qutefox/SensorFusion/software/src/processor_logic/fusion_data.cpp

#include "fusion_data.h"

#include "mxc_lock.h"

#include "src/storage/register_map.h"
#include "src/sensor_fusion_board.h"
#include "src/sensor/lsm6dsm.h"
#include "src/debug_print.h"

FusionData* FusionData::instance = nullptr;
uint32_t FusionData::lock = 0;

FusionData::FusionData()
    : register_map{ storage::RegisterMap::get_instance() }
    , register_map_helper{ storage::RegisterMapHelper::get_instance(register_map) }
    , calibration_data{ CalibrationData::get_instance() }
    , quaternion_fqvect{ FUSION_IDENTITY_QUATERNION }
    , euler{ FUSION_EULER_ZERO }
    , earth{ FUSION_VECTOR_ZERO }
    , gyroscope_fvect{ FUSION_VECTOR_ZERO }
    , accelerometer_fvect{ FUSION_VECTOR_ZERO }
    , magnetometer_fvect{ FUSION_VECTOR_ZERO }
    , pressure{ 0 }
    , temperature{ 0 }
    , timestamp{ 0 }
    , previous_timestamp{ 0 }
    , has_new_quaternion_data{ false }
    , has_new_euler_data{ false }
    , has_new_earth_data{ false }
    , has_new_pressure_data{ false }
    , has_new_temperature_data{ false }
    , has_new_gyroscope_data{ false }
    , has_new_accelerometer_data{ false }
    , has_new_magnetometer_data{ false }
    , use_calibration_data{ false }
    , euler_output_enabled{ false }
    , earth_output_enabled{ false }
    , ahrs_error{ false }
    , ahrs_gyro_error{ false }
    , ahrs_accel_error{ false }
    , ahrs_mag_error{ false }
{
    FusionAhrsInitialise(&ahrs);

    if (CONTROL1_REGISTER_DEFAULT_VALUE & CONTROL1_REGISTER_EULER_MASK)
    {
        euler_output_enabled = true;
    }

    if (CONTROL1_REGISTER_DEFAULT_VALUE & CONTROL1_REGISTER_EARTH_MASK)
    {
        earth_output_enabled = true;
    }

    if (CONTROL2_REGISTER_DEFAULT_VALUE & CONTROL2_REGISTER_CALIBRATION_ACTIVE_MASK)
    {
        use_calibration_data = true;
    }

    update_calibration_data();

    // Cannot call reset here, because the SensorBase class constructs the fusion data (this class)
    // before the SensorFusionBoard class does.
    // Meaning that the board pointer is nullptr here and now.
    // Inside the reset() function we use the board class to get the sensor pointer
    // to read the data rate (board->inertial_sensor->get_data_rate()).
    // This causes a nullpointer exception.
    // The Controller class will call reset when starting the fusion.
    // reset();
}

FusionData::~FusionData()
{
    FusionAhrsReset(&ahrs);
}

FusionData* FusionData::get_instance()
{
    MXC_GetLock(&lock, 1);
    if (instance == nullptr)
    {
        instance = new FusionData();
    }
    MXC_FreeLock(&lock);
    return instance;
}

void FusionData::reset()
{
    uint16_t gyro_sample_rate = 100;

    sensor::SensorInterface* sensor = nullptr;
    SensorFusionBoard* board = SensorFusionBoard::get_instance();
    if (board != nullptr)
    {
        sensor = board->get_inertial_sensor();
    }
    
    if (sensor != nullptr)
    {
        gyro_sample_rate = sensor->get_sample_rate_in_hz(sensor::Lsm6dsmDevice::LSM6DSM_DEVICE_GYRO);
        if (gyro_sample_rate == 0) gyro_sample_rate = 100;
    }

    FusionOffsetInitialise(&ahrs_offset, gyro_sample_rate);

    // Set AHRS algorithm settings.
    const FusionAhrsSettings settings = {
        .convention = FusionConventionNwu,
        .gain = 0.5f,
        .gyroscopeRange = 500.0f, // gyroscope range in degrees/s
        .accelerationRejection = 10.0f,
        .magneticRejection = 10.0f,
        .recoveryTriggerPeriod = 5 * gyro_sample_rate, // 5 seconds
    };
    FusionAhrsSetSettings(&ahrs, &settings);

    FusionAhrsReset(&ahrs);
    
    has_new_quaternion_data = false;
    has_new_euler_data = false;
    has_new_earth_data = false;
    has_new_pressure_data = false;
    has_new_temperature_data = false;
    has_new_gyroscope_data = false;
    has_new_accelerometer_data = false;
    has_new_magnetometer_data = false;

    ahrs_error = false;
    ahrs_gyro_error = false;
    ahrs_accel_error = false;
    ahrs_mag_error = false;
}

void FusionData::update_register_map()
{
    if (register_map_helper->is_quaternion_data_read_by_host())
    {
        if (has_new_quaternion_data)
        {
            register_map_helper->write_quaternion_data(quaternion_fqvect);
            has_new_quaternion_data = false;
            register_map_helper->set_quaternion_data_ready_flag(true);
        }
        else
        {
            register_map_helper->set_quaternion_data_ready_flag(false);
        }
    }

    if (register_map_helper->is_euler_data_read_by_host())
    {
        if (has_new_euler_data)
        {
            register_map_helper->write_euler_data(euler);
            has_new_euler_data = false;
            register_map_helper->set_euler_data_ready_flag(true);
        }
        else
        {
            register_map_helper->set_euler_data_ready_flag(false);
        }
    }

    if (register_map_helper->is_earth_data_read_by_host())
    {
        if (has_new_earth_data)
        {
            register_map_helper->write_earth_data(earth);
            has_new_earth_data = false;
            register_map_helper->set_earth_data_ready_flag(true);
        }
        else
        {
            register_map_helper->set_earth_data_ready_flag(false);
        }
    }

    if (register_map_helper->is_gyroscope_data_read_by_host())
    {
        if (has_new_gyroscope_data)
        {
            register_map_helper->write_gyroscope_data(gyroscope_fvect);
            has_new_gyroscope_data = false;
            register_map_helper->set_gyroscope_data_ready_flag(true);
        }
        else
        {
            register_map_helper->set_gyroscope_data_ready_flag(false);
        }
    }

    if (register_map_helper->is_accelerometer_data_read_by_host())
    {
        if (has_new_accelerometer_data)
        {
            register_map_helper->write_accelerometer_data(accelerometer_fvect);
            has_new_accelerometer_data = false;
            register_map_helper->set_accelerometer_data_ready_flag(true);
        }
        else
        {
            register_map_helper->set_accelerometer_data_ready_flag(false);
        }
    }

    if (register_map_helper->is_magnetometer_data_read_by_host())
    {
        if (has_new_magnetometer_data)
        {
            register_map_helper->write_magnetometer_data(magnetometer_fvect);
            has_new_magnetometer_data = false;
            register_map_helper->set_magnetometer_data_ready_flag(true);
        }
        else
        {
            register_map_helper->set_magnetometer_data_ready_flag(false);
        }
    }

    if (register_map_helper->is_pressure_data_read_by_host())
    {
        if (has_new_pressure_data)
        {
            register_map_helper->write_pressure_data(pressure);
            has_new_pressure_data = false;
            register_map_helper->set_pressure_data_ready_flag(true);
        }
        else
        {
            register_map_helper->set_pressure_data_ready_flag(false);
        }
    }

    if (register_map_helper->is_temperature_data_read_by_host())
    {
        if (has_new_temperature_data)
        {
            register_map_helper->write_temperature_data(temperature);
            has_new_temperature_data = false;
            register_map_helper->set_temperature_data_ready_flag(true);
        }
        else
        {
            register_map_helper->set_temperature_data_ready_flag(false);
        }
    }
}

void FusionData::set_use_calibration_data(bool use)
{
    use_calibration_data = use;
}

void FusionData::set_euler_output_enable(bool enable)
{
    if (!enable)
    {
        register_map_helper->set_euler_data_ready_flag(false);
        has_new_euler_data = false;
        euler = FUSION_EULER_ZERO;
    }
    euler_output_enabled = enable;
}

void FusionData::set_earth_output_enable(bool enable)
{
    if (!enable)
    {
        register_map_helper->set_earth_data_ready_flag(false);
        has_new_earth_data = false;
        earth = FUSION_VECTOR_ZERO;
    }
    earth_output_enabled = enable;
}

void FusionData::update_calibration_data()
{
    gyroscope_misalignment = calibration_data->get_gyroscope_misalignment();
    gyroscope_sensitivity = calibration_data->get_gyroscope_sensitivity();
    gyroscope_offset = calibration_data->get_gyroscope_offset();

    accelerometer_misalignment = calibration_data->get_accelerometer_misalignment();
    accelerometer_sensitivity = calibration_data->get_accelerometer_sensitivity();
    accelerometer_offset = calibration_data->get_accelerometer_offset();

    soft_iron_matrix = calibration_data->get_soft_iron_matrix();
    hard_iron_offset = calibration_data->get_hard_iron_offset();
}

void FusionData::update_fusion()
{
    // This method should be called repeatedly each time new gyroscope data is available.
    // Update gyroscope AHRS algorithm.
    FusionAhrsUpdate(&ahrs, gyroscope_fvect, accelerometer_fvect, magnetometer_fvect, get_time_delta_in_seconds());

    ahrs_flags = FusionAhrsGetFlags(&ahrs);

    bool current_ahrs_error = false;
    if (ahrs_flags.angularRateRecovery)
    {
        register_map_helper->set_gyroscope_sensor_error(true);
        ahrs_gyro_error = true;
        current_ahrs_error = true;
    }
    else if (ahrs_gyro_error)
    {
        register_map_helper->set_gyroscope_sensor_error(false);
        ahrs_gyro_error = false;
    }

    if (ahrs_flags.accelerationRecovery)
    {
        register_map_helper->set_accelerometer_sensor_error(true);
        ahrs_accel_error = true;
        current_ahrs_error = true;
    }
    else if (ahrs_accel_error)
    {
        register_map_helper->set_accelerometer_sensor_error(false);
        ahrs_accel_error = false;
    }

    if (ahrs_flags.magneticRecovery)
    {
        register_map_helper->set_magnetometer_sensor_error(true);
        ahrs_mag_error = true;
        current_ahrs_error = true;
    }
    else if (ahrs_mag_error)
    {
        register_map_helper->set_magnetometer_sensor_error(false);
        ahrs_mag_error = false;
    }

    if (current_ahrs_error != ahrs_error)
    {
        ahrs_error = current_ahrs_error;
        register_map_helper->set_fusion_error(ahrs_error);

        // Hmm, should we not provide output data?!
        // For the time being, try to give something to the user.
        // We might change this in the future when we are older and wiser.
    }

    if (ahrs_flags.initialising)
    {
        // Only provide output data after init is done.
        return;
    }
    
    quaternion_fqvect = FusionAhrsGetQuaternion(&ahrs);
    has_new_quaternion_data = true;

    if (euler_output_enabled)
    {
        euler =  FusionQuaternionToEuler(quaternion_fqvect);
        has_new_euler_data = true;
    }

    if (earth_output_enabled)
    {
        earth = FusionAhrsGetEarthAcceleration(&ahrs);
        has_new_earth_data = true;
    }
}

void FusionData::update_gyroscope(const FusionVector& gyroscope_data)
{
    gyroscope_fvect = gyroscope_data;
    if (use_calibration_data)
    {
        // Apply calibration.
        gyroscope_fvect = FusionCalibrationInertial(gyroscope_fvect, gyroscope_misalignment, gyroscope_sensitivity, gyroscope_offset);
        // Update gyroscope offset correction algorithm
        gyroscope_fvect = FusionOffsetUpdate(&ahrs_offset, gyroscope_fvect);
    }
    has_new_gyroscope_data = true;
    update_fusion();
}

void FusionData::update_accelerometer(const FusionVector& accelerometer_data)
{
    accelerometer_fvect = accelerometer_data;
    if (use_calibration_data)
    {
        // Apply calibration.
        accelerometer_fvect = FusionCalibrationInertial(accelerometer_fvect, accelerometer_misalignment, accelerometer_sensitivity, accelerometer_offset);
    }
    has_new_accelerometer_data = true;
}

void FusionData::update_magnetometer(const FusionVector& magnetometer_data)
{
    magnetometer_fvect = magnetometer_data;
    if (use_calibration_data)
    {
        // Apply calibration.
        magnetometer_fvect = FusionCalibrationMagnetic(magnetometer_fvect, soft_iron_matrix, hard_iron_offset);
    }
    has_new_magnetometer_data = true;
}

void FusionData::update_pressure(sensor::pressure_t pressure_data)
{
    pressure = pressure_data;
    has_new_pressure_data = true;
}

void FusionData::update_temperature(sensor::temperature_t temperature_data)
{
    temperature.i16bit = (temperature.i16bit/2) + (temperature_data.i16bit/2);
    has_new_temperature_data = true;
}

void FusionData::update_timestamp(sensor::timestamp_t timestamp_data)
{
    timestamp = timestamp_data;
}

float FusionData::get_time_delta_in_seconds() // in seconds
{
    // We multiply by 25 because the timestamp generation (in LSM6DSM) has 25 microsecond resolution set.
    uint32_t diff_microseconds = (timestamp.u32bit - previous_timestamp.u32bit) * 25;
    previous_timestamp = timestamp;
    return static_cast<float>(diff_microseconds) / 1000000; // Convert microsecond to second.
}
