qutefox/SensorFusion/software/src/io/i2c_slave.h

#pragma once

#include "mxc_device.h"
#include "i2c.h"

#include "src/storage/register_interface.h"
#include "src/io/i2c_slave_interface.h"

#define I2C_SLAVE_MAX_DATA_RX 64
#define I2C_SLAVE_ADDR_SIZE sizeof(uint8_t)
#define I2C_SLAVE_RX_BUF_SIZE (I2C_SLAVE_MAX_DATA_RX + I2C_SLAVE_ADDR_SIZE)

namespace io
{

class I2cSlave : public I2cSlaveInterface
{
private:
    static I2cSlave* instance;
    static uint32_t lock;

    uint8_t address;
	bool write_op; // Read/write operation state variable
	uint8_t num_rx; // Number of characters in rx_buf
	uint8_t rx_buf[I2C_SLAVE_RX_BUF_SIZE]; // Buffer to store received characters
    uint8_t tx_byte = 0;
	bool overflow; // Rx buffer overflowed during transaction
    volatile bool transaction_done = false;
    storage::MultiRegisterInterface<uint8_t, uint8_t>* register_map; // Oddly we use raw pointer and not interface.
    volatile bool read_flag = false;
    volatile bool write_flag = false;

    int event_handler(mxc_i2c_regs_t* i2c, mxc_i2c_slave_event_t event, void* retVal);

    void reset_state();

    void send_data();
    void receive_data();
    void store_data();
    void transaction_complete(int err);

protected:
    I2cSlave();
    virtual ~I2cSlave();

public:
    I2cSlave(I2cSlave& other) = delete;
    void operator=(const I2cSlave& other) = delete;

    static I2cSlave* get_instance();

    virtual int begin(uint8_t slave_address) override;
    int prepare_for_next_transaction();
    virtual bool is_current_transaction_done() const override { return transaction_done; }
    virtual bool has_got_read_request() override;
    virtual bool has_got_write_request() override;
};

} // namespace io
