qutefox/SensorFusion/software/src/io/digital_output_pin.cpp

#include "digital_output_pin.h"

#include "mxc_errors.h"

using namespace io;

DigitalOutputPin::DigitalOutputPin(mxc_gpio_regs_t *pin_port, uint32_t pin_mask, mxc_gpio_drvstr_t drive_strength)
{
    gpio.port = pin_port;
    gpio.mask = pin_mask;
    gpio.drvstr = drive_strength;
	gpio.pad = MXC_GPIO_PAD_NONE;
	gpio.func = MXC_GPIO_FUNC_OUT;

    MXC_GPIO_Config(&gpio);
}

DigitalOutputPin::~DigitalOutputPin()
{
    MXC_GPIO_Shutdown(gpio.mask);
}

int DigitalOutputPin::write(bool value)
{
    if (value) MXC_GPIO_OutSet(gpio.port, gpio.mask);
    else MXC_GPIO_OutClr(gpio.port, gpio.mask);
    return E_NO_ERROR;
}

int DigitalOutputPin::read(bool& value)
{
    value = false;
    if (MXC_GPIO_OutGet(gpio.port, gpio.mask)) value = true;
    return E_NO_ERROR;
}

int DigitalOutputPin::toggle()
{
    MXC_GPIO_OutToggle(gpio.port, gpio.mask);
    return E_NO_ERROR;
}
